Protocentral/Pulse_MAX30102/extras/4806.jpg

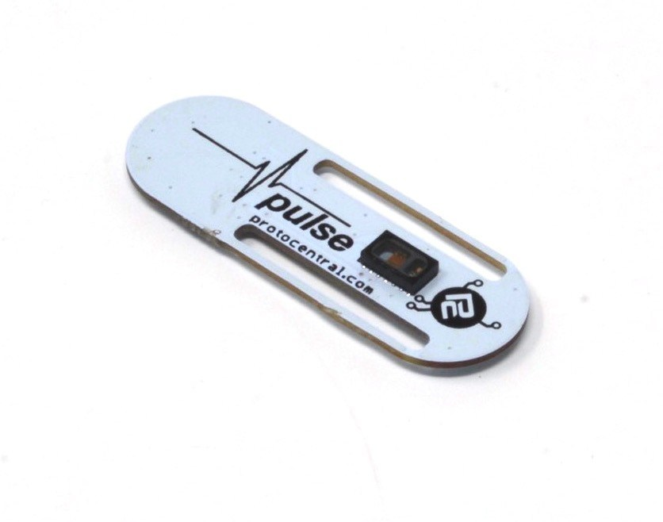
extras/4806.jpg
